ioios-io/pithy/Cases/step/Pithy Screen Plus/Pithy Screen Plus Slanted Stand.step

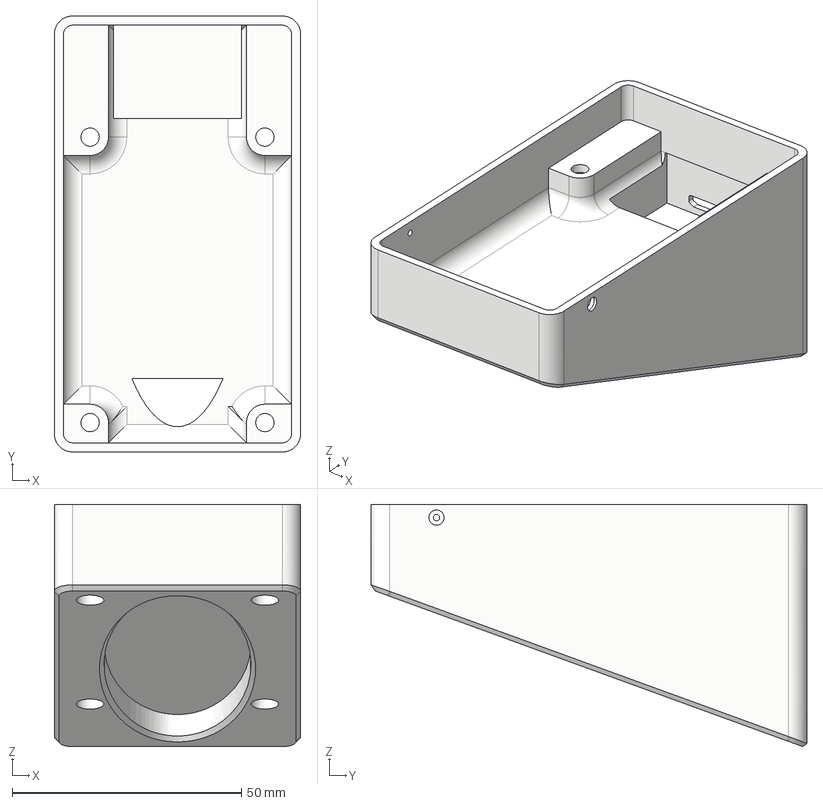
[picture p18: CAD file, 2021-06-20]
Cases/step/Pithy Screen Plus/Pithy Screen Plus Slanted Stand.step
53.7 x 95.0 x 52.8 mm
