ioios-io/pithy/Cases/step/Pithy Screen/Pithy Screen Mount C.step

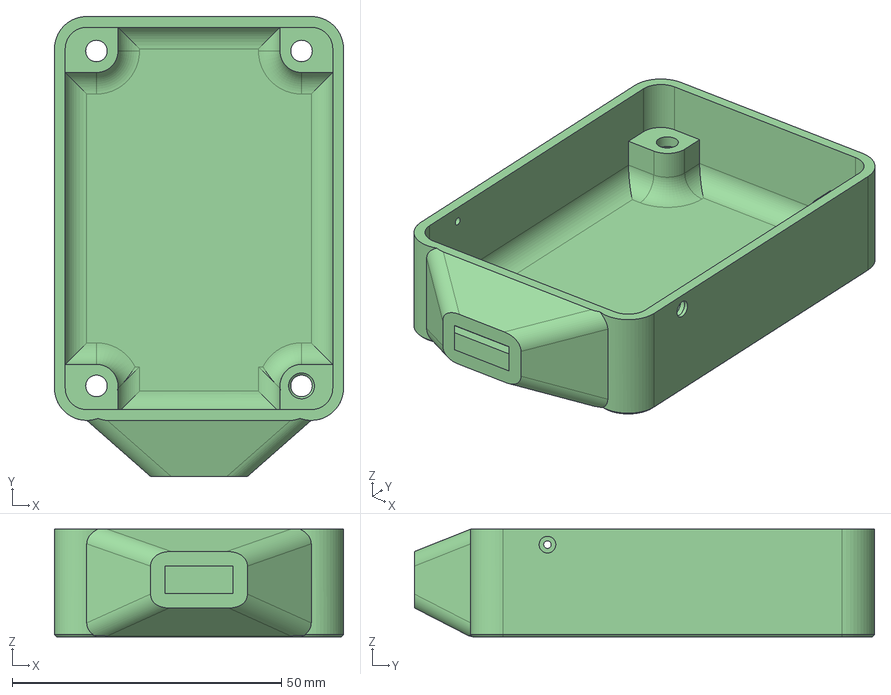
[picture p19: CAD file, 2021-07-11]
Cases/step/Pithy Screen/Pithy Screen Mount C.step
53.7 x 85.5 x 20.0 mm
