ioios-io/pithy/Cases/step/Pithy Dial Plus/Pithy Dial Plus Mount C.step

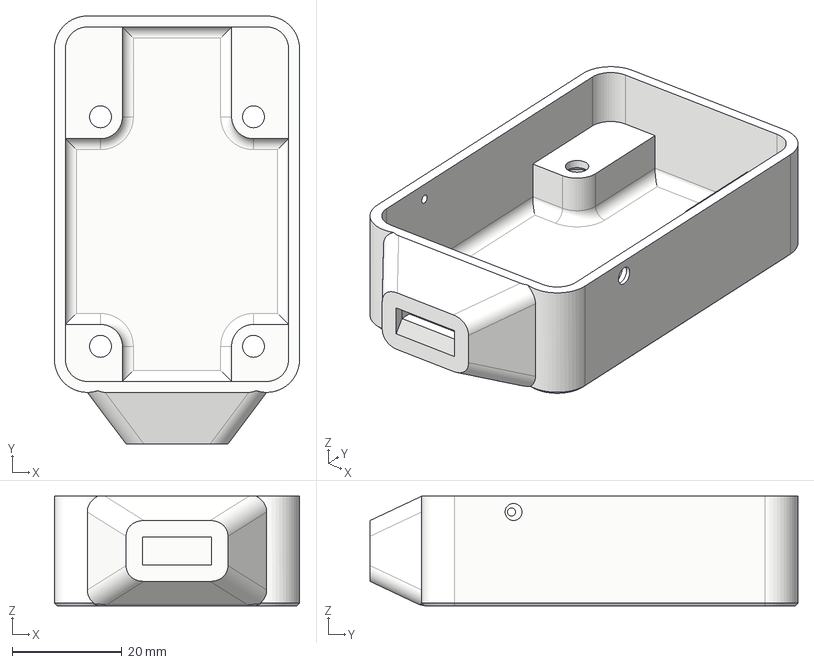
[picture p20: CAD file, 2021-03-28]
Cases/step/Pithy Dial Plus/Pithy Dial Plus Mount C.step
44.8 x 78.2 x 20.0 mm
