ioios-io/pithy/Cases/step/Pithy Dial/Pithy Dial Mount B.step

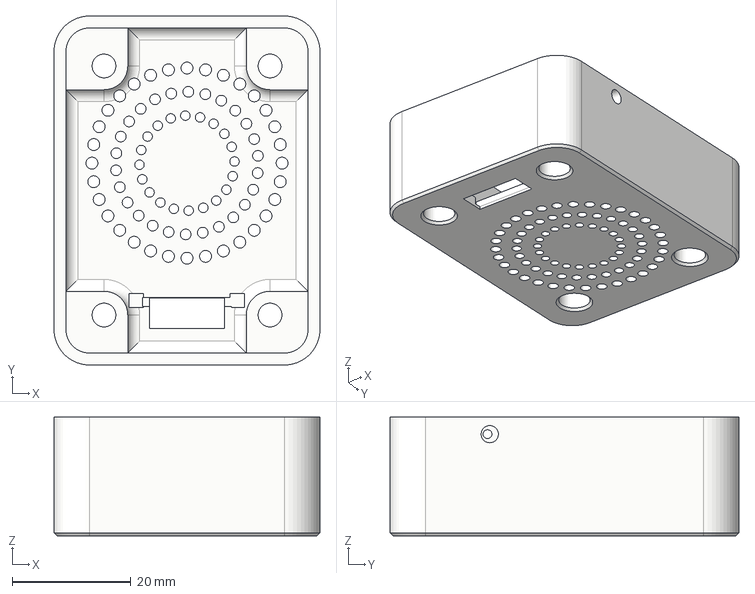
[picture p21: CAD file, 2021-03-28]
Cases/step/Pithy Dial/Pithy Dial Mount B.step
44.8 x 58.7 x 20.0 mm
