ioios-io/pithy/Cases/step/Pithy Pixel Plus/Pithy Pixel Plus Faceplate.step

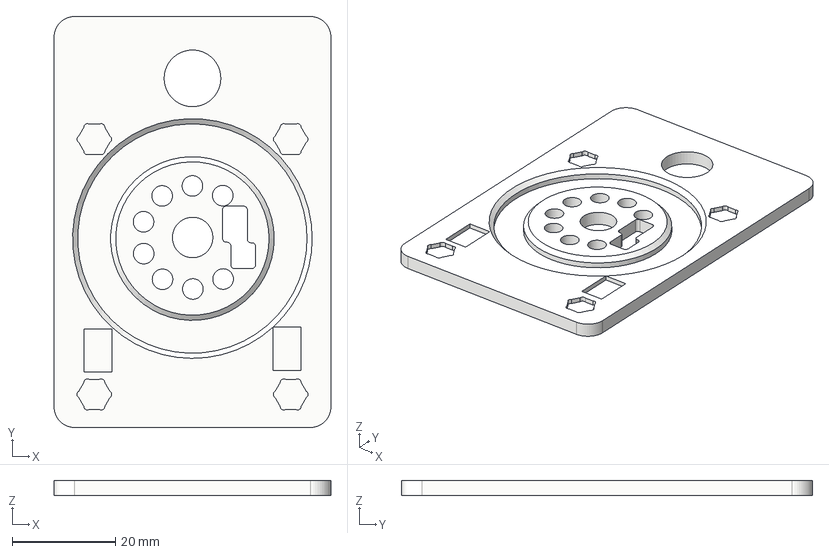
[picture p22: CAD file, 2021-06-11]
Cases/step/Pithy Pixel Plus/Pithy Pixel Plus Faceplate.step
53.7 x 79.8 x 3.00 mm
