ioios-io/pithy/Cases/step/Pithy Pixel/Pithy Pixel Faceplate.step

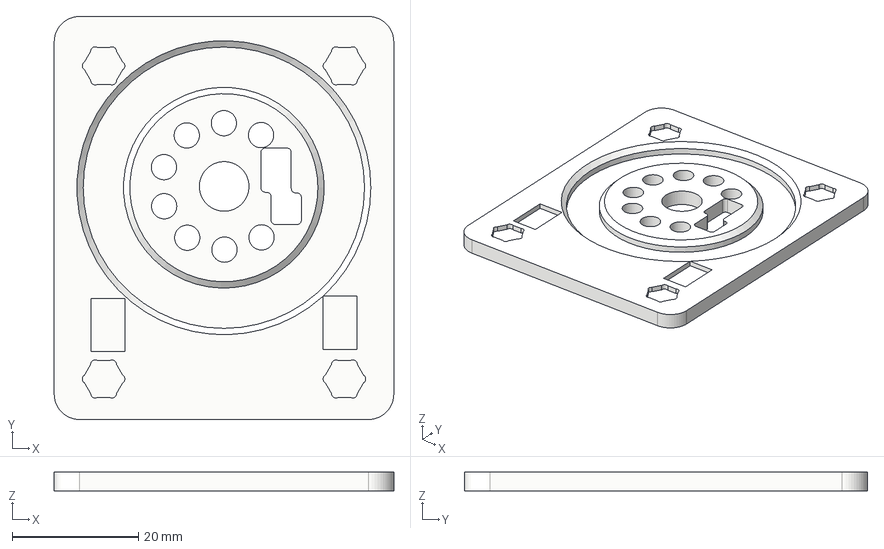
[picture p23: CAD file, 2021-06-11]
Cases/step/Pithy Pixel/Pithy Pixel Faceplate.step
53.7 x 63.8 x 3.00 mm
