ioios-io/pithy/Cases/step/Pithy Screen Plus/Pithy Screen Plus Faceplate.step

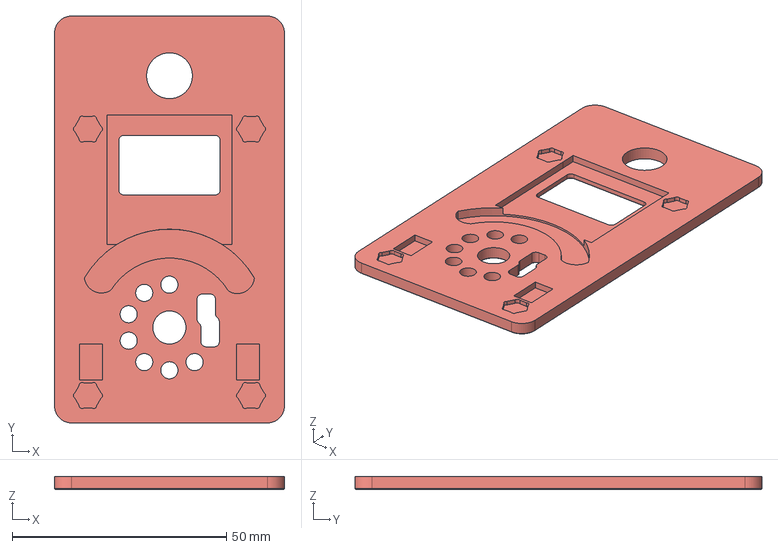
[picture p24: CAD file, 2021-06-11]
Cases/step/Pithy Screen Plus/Pithy Screen Plus Faceplate.step
53.7 x 95.0 x 3.00 mm
