ioios-io/pithy/Cases/step/Pithy Screen/Pithy Screen Mount A.step

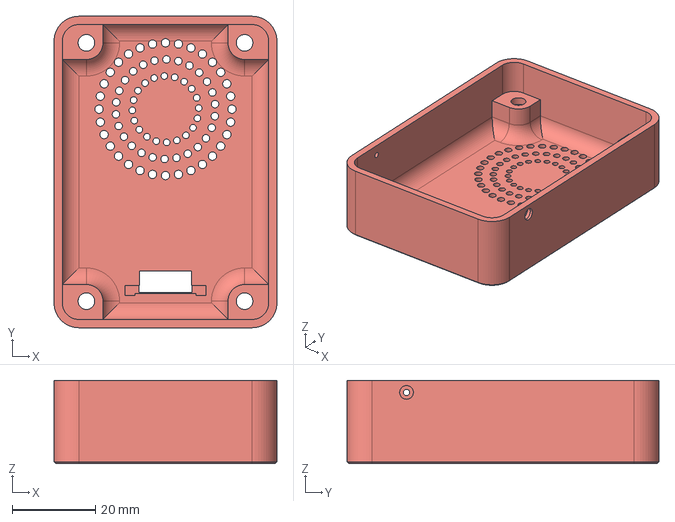
[picture p25: CAD file, 2021-07-11]
Cases/step/Pithy Screen/Pithy Screen Mount A.step
53.7 x 75.0 x 20.0 mm
