ioios-io/pithy/Cases/stl/Pithy Pixel Plus/Printed Knob Standard.stl

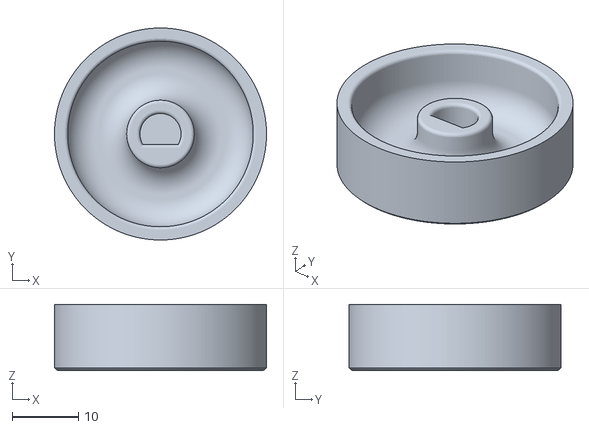
[picture p26: CAD file, 2020-12-21]
Cases/stl/Pithy Pixel Plus/Printed Knob Standard.stl
32.0 x 32.0 x 10.0
