ioios-io/pithy/Cases/stl/Pithy Screen/Printed Knob Standard.stl

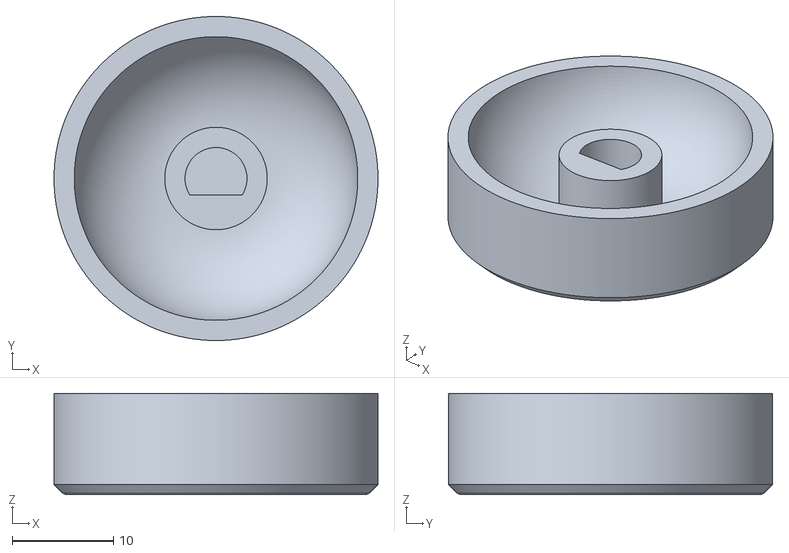
[picture p27: CAD file, 2020-12-08]
Cases/stl/Pithy Screen/Printed Knob Standard.stl
32.0 x 32.0 x 10.0
