ioios-io/pithy/Cases/step/Pithy Dial Plus/Pithy Dial Plus Mount B.step

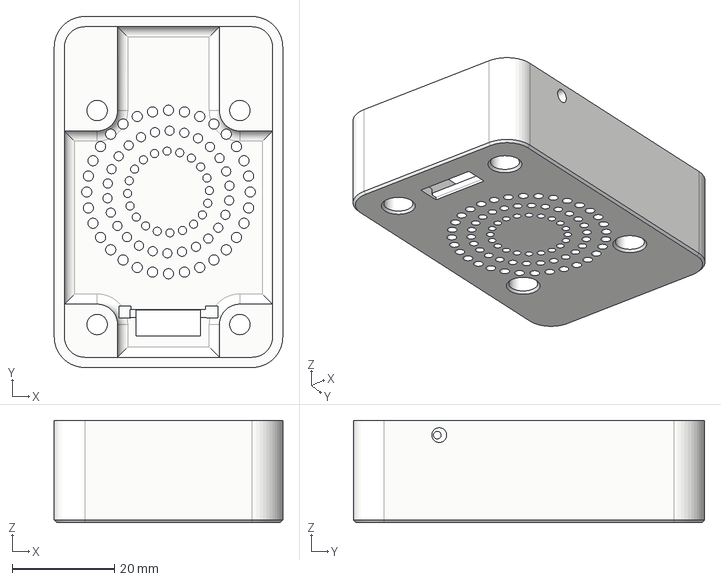
[picture p28: CAD file, 2021-03-28]
Cases/step/Pithy Dial Plus/Pithy Dial Plus Mount B.step
44.8 x 68.7 x 20.0 mm
