ioios-io/pithy/Cases/step/Pithy PIxel Multi Mount.step

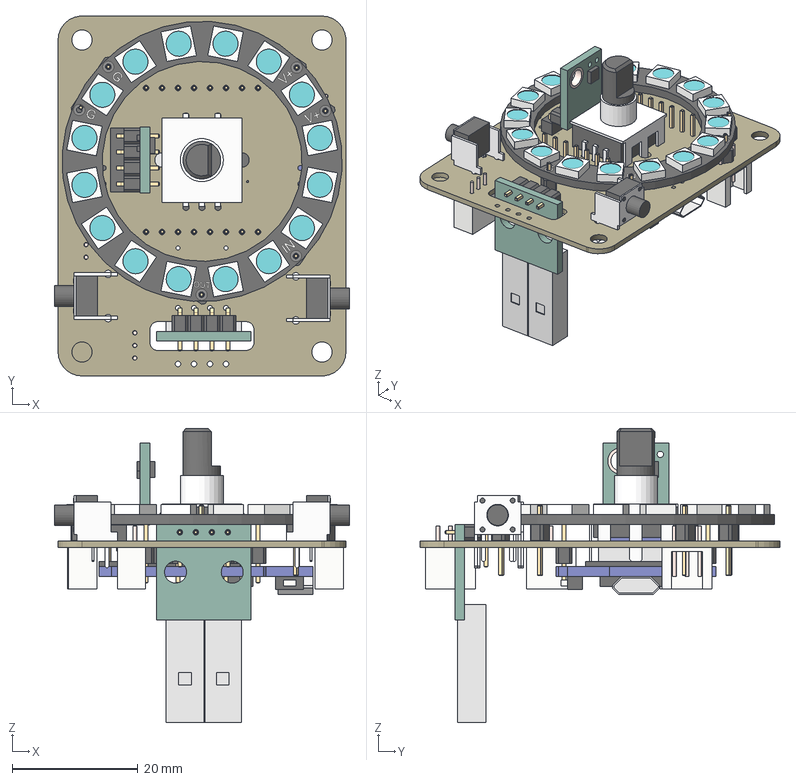
[picture p29: CAD file, 2021-03-28]
Cases/step/Pithy PIxel Multi Mount.step
46.8 x 57.2 x 46.7 mm
Pin Headers Right Angled v5
Board
Neopixel v1 x 16
Pin Headers v7 x 6
PADS_4
Pin Headers v3 x 2
HOLE_3.2 x 4
ROTARY_ENCODER
Pin Headers Right Angled v3
OSHW-LOGO-M
OSHW-LOGO-S
SPDT_RIGHT_ANGLE x 2
