ioios-io/pithy/Cases/step/Pithy Pixel Plus/Pithy Pixel Plus Mount A.step

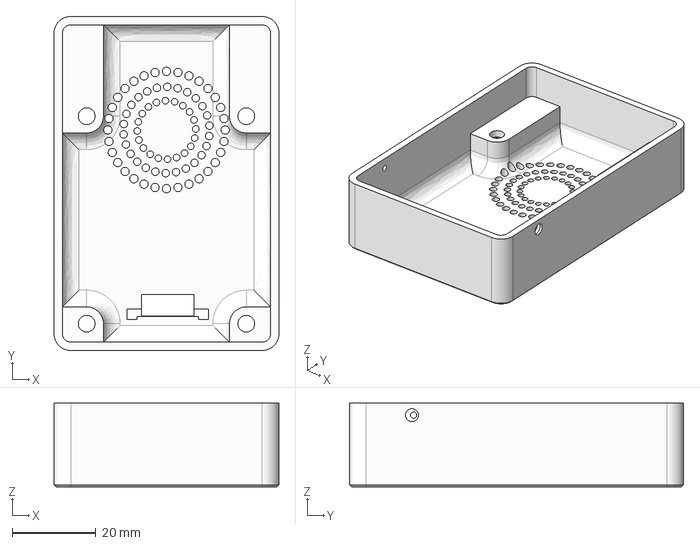
[picture p30: CAD file, 2021-03-28]
Cases/step/Pithy Pixel Plus/Pithy Pixel Plus Mount A.step
53.7 x 79.8 x 20.0 mm
