ioios-io/pithy/Cases/step/Pithy Pixel/Pithy Pixel Mount B.step

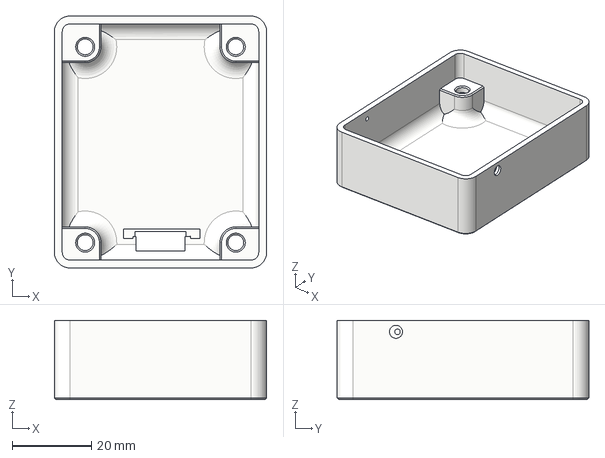
[picture p31: CAD file, 2021-03-28]
Cases/step/Pithy Pixel/Pithy Pixel Mount B.step
53.7 x 63.8 x 20.0 mm
