ioios-io/pithy/Cases/step/Pithy Screen Plus/Pithy Screen Plus Mount B.step

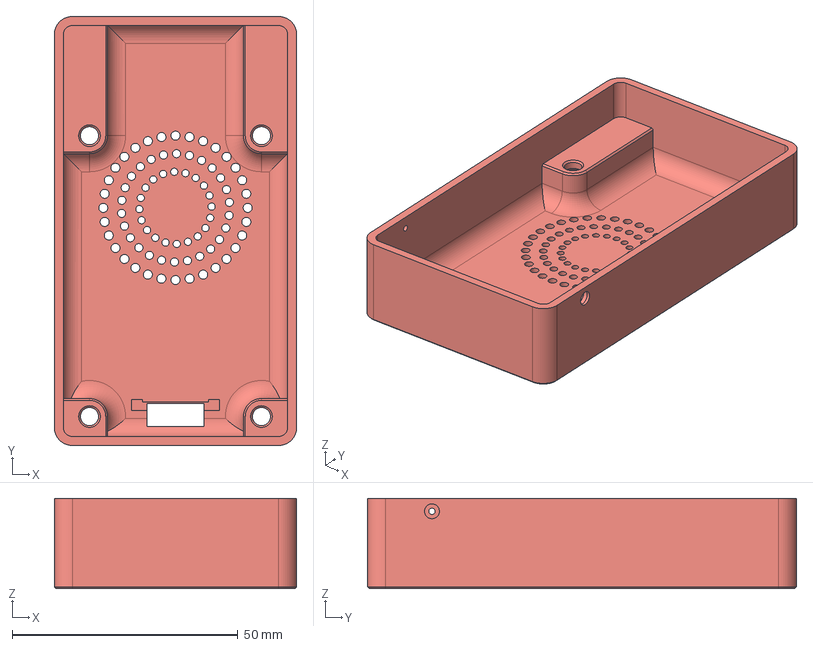
[picture p32: CAD file, 2021-03-28]
Cases/step/Pithy Screen Plus/Pithy Screen Plus Mount B.step
53.7 x 95.0 x 20.0 mm
