ioios-io/pithy/Cases/step/Pithy Screen/Pithy Screen Straight Stand.step

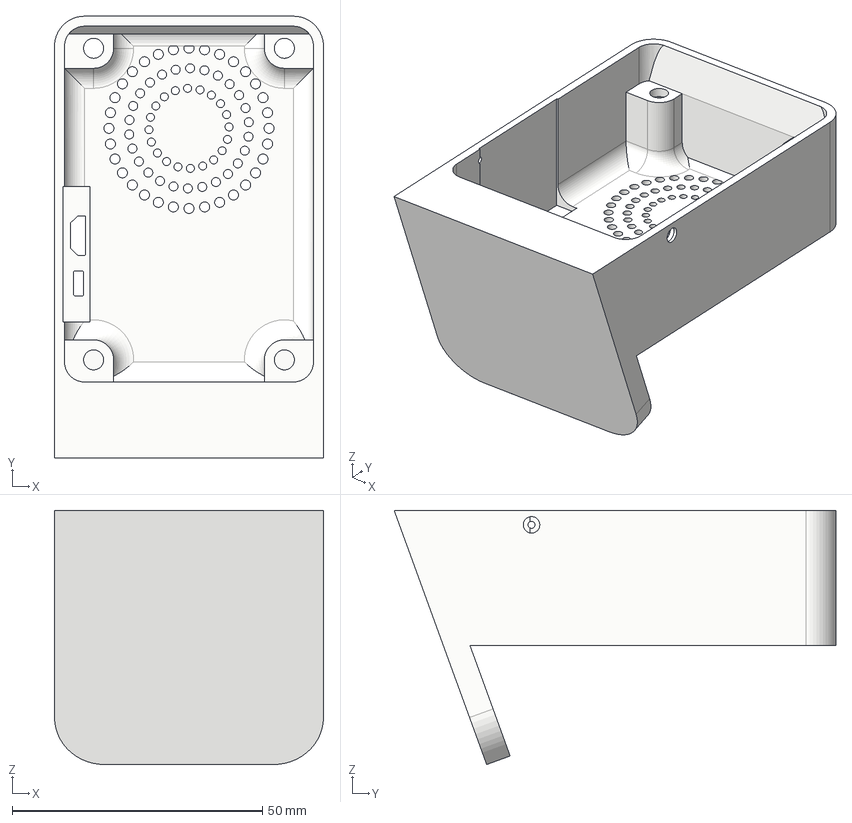
[picture p33: CAD file, 2021-07-03]
Cases/step/Pithy Screen/Pithy Screen Straight Stand.step
53.7 x 88.2 x 50.7 mm
