ioios-io/pithy/Cases/step/Pithy Dial Multi Mount.step

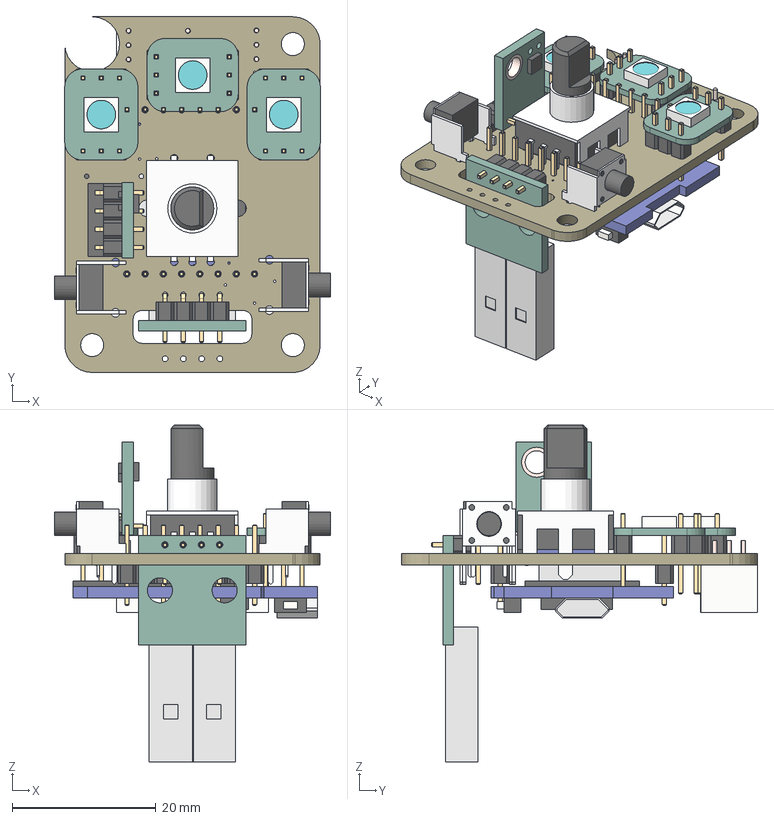
[picture p34: CAD file, 2021-03-28]
Cases/step/Pithy Dial Multi Mount.step
38.5 x 49.6 x 46.9 mm
Board
Pin Headers v3 x 2
HOLE_3.2 x 4
Neopixel v1 x 3
Pin Headers v10 x 6
Pin Headers Right Angled v3
ROTARY_ENCODER
SPDT_RIGHT_ANGLE x 2
OSHW-LOGO-M
OSHW-LOGO-S
Pin Headers Right Angled v5
