ioios-io/pithy/Cases/step/Pithy Dial/Pithy Dial Mount C.step

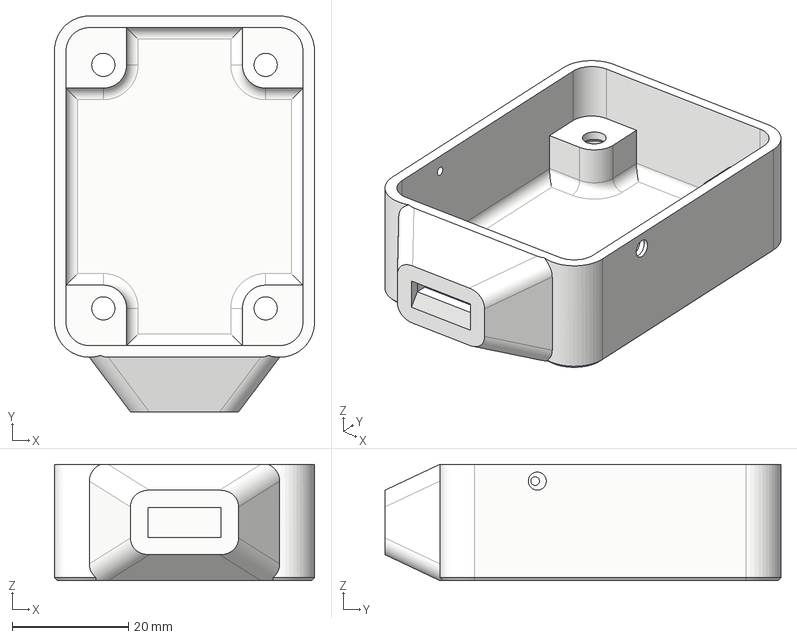
[picture p35: CAD file, 2021-03-28]
Cases/step/Pithy Dial/Pithy Dial Mount C.step
44.8 x 68.2 x 20.0 mm
