ioios-io/pithy/Cases/step/Pithy Pixel/Pithy Pixel Mount C.step

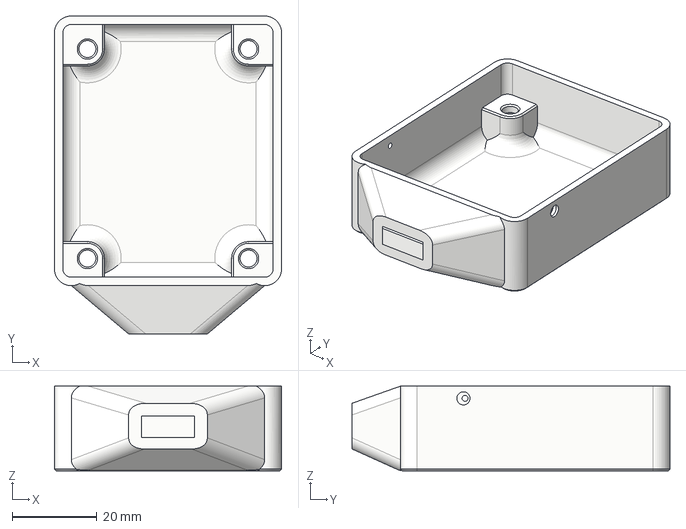
[picture p36: CAD file, 2021-03-28]
Cases/step/Pithy Pixel/Pithy Pixel Mount C.step
53.7 x 75.2 x 20.0 mm
