ioios-io/pithy/Cases/step/Pithy Screen Plus/Pithy Screen Plus Mount C.step

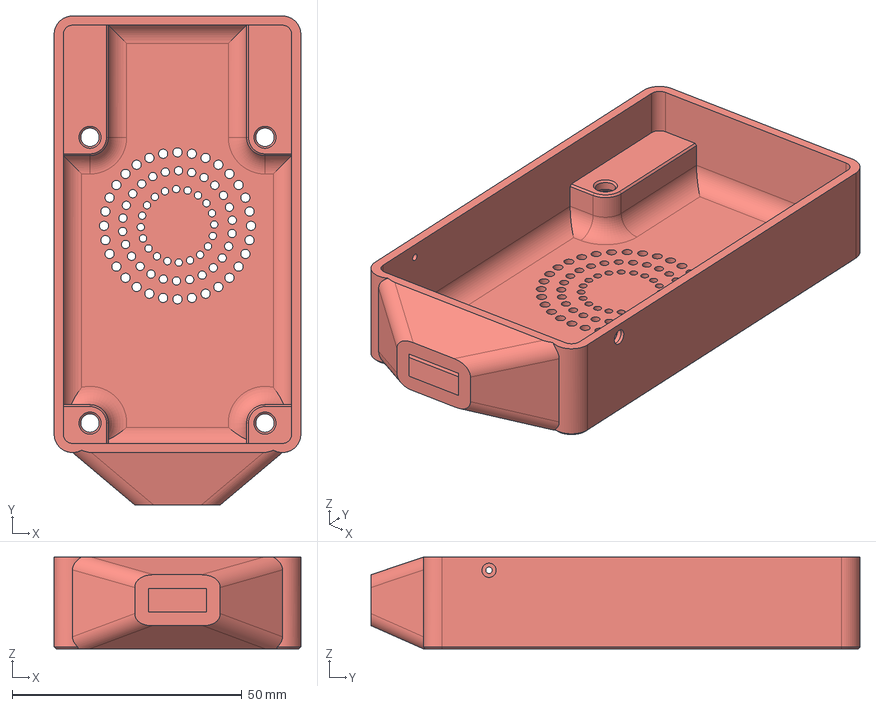
[picture p37: CAD file, 2021-03-28]
Cases/step/Pithy Screen Plus/Pithy Screen Plus Mount C.step
53.7 x 106.5 x 20.0 mm
