ioios-io/pithy/Cases/step/Pithy Screen/Pithy Screen Slanted Stand.step

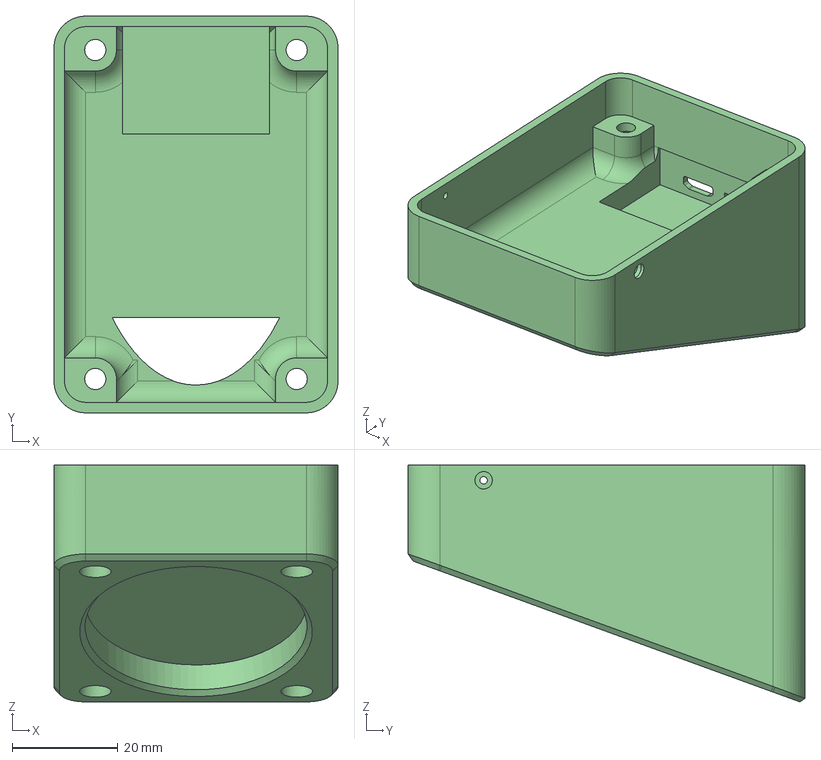
[picture p38: CAD file, 2021-06-20]
Cases/step/Pithy Screen/Pithy Screen Slanted Stand.step
53.7 x 75.0 x 44.8 mm
