ioios-io/pithy/Cases/step/Pithy Pixel Plus/Pithy Pixel Plus Mount D.step

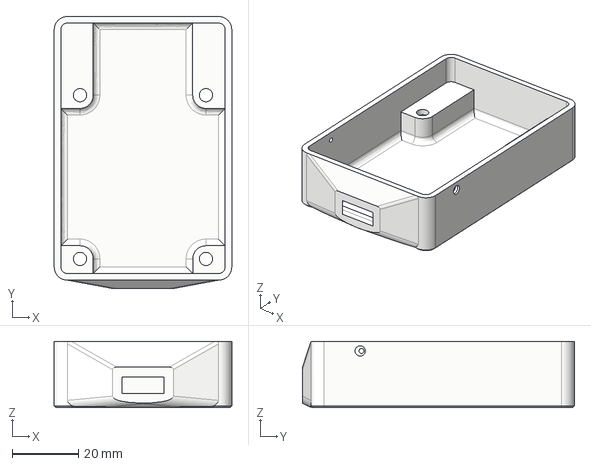
[picture p39: CAD file, 2021-03-28]
Cases/step/Pithy Pixel Plus/Pithy Pixel Plus Mount D.step
53.7 x 82.3 x 20.0 mm
