ioios-io/pithy/Cases/step/Pithy Pixel/Pithy Pixel Mount D.step

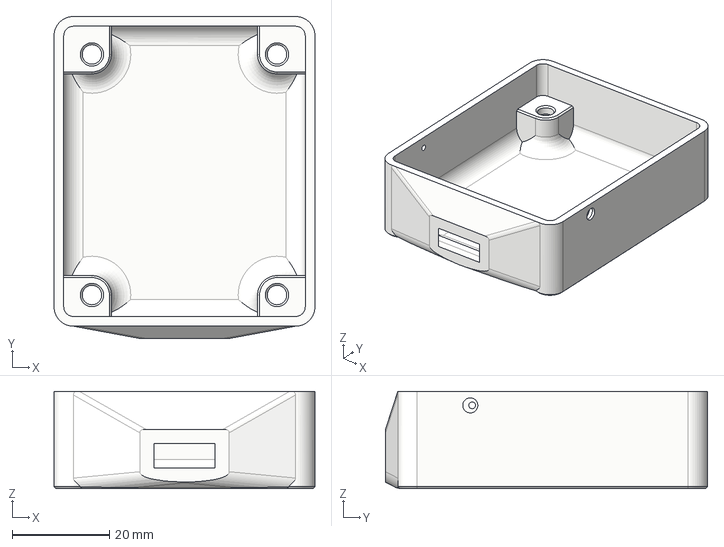
[picture p40: CAD file, 2021-03-28]
Cases/step/Pithy Pixel/Pithy Pixel Mount D.step
53.7 x 66.3 x 20.0 mm
