ioios-io/pithy/Cases/step/Pithy Screen Multi Mount.step

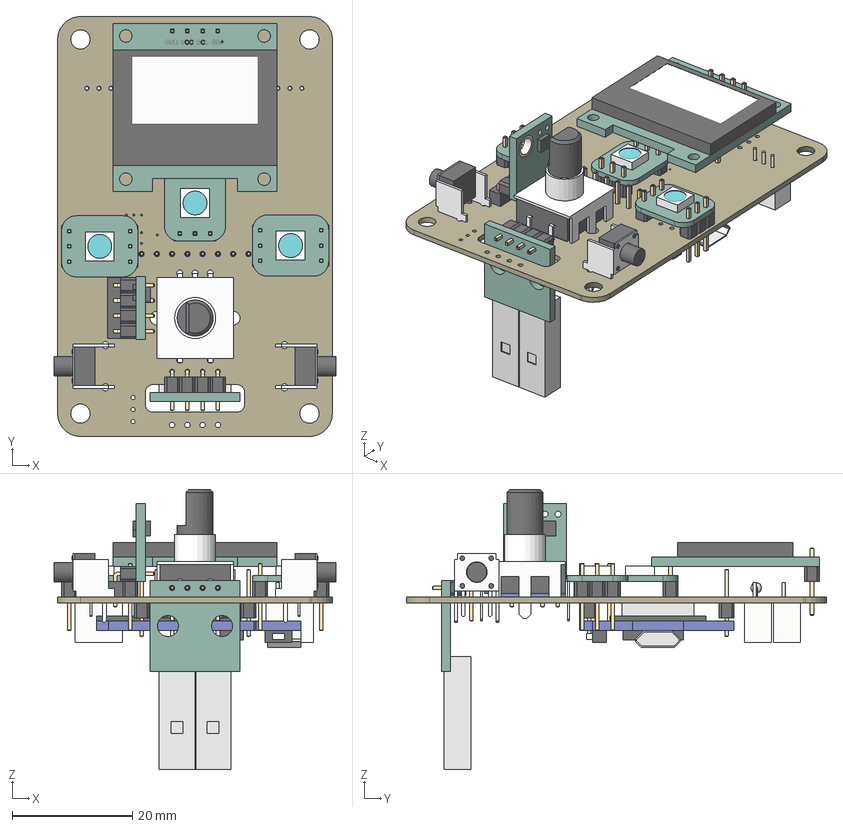
[picture p41: CAD file, 2021-03-28]
Cases/step/Pithy Screen Multi Mount.step
46.8 x 69.9 x 46.6 mm
Board
HOLE_3.2 x 4
ROTARY_ENCODER
1/4W_RESISTOR
Pin Headers v3 x 2
Neopixel v1 x 3
Pin Headers v10 x 6
Pin Headers v2
PADS_4
SPDT_RIGHT_ANGLE x 2
Pin Headers Right Angled v3
OSHW-LOGO-L
OSHW-LOGO-M
OSHW-LOGO-S
Pin Headers Right Angled v5 (2)
