ioios-io/pithy/Cases/step/Pithy Screen Plus/Pithy Screen Plus Mount D.step

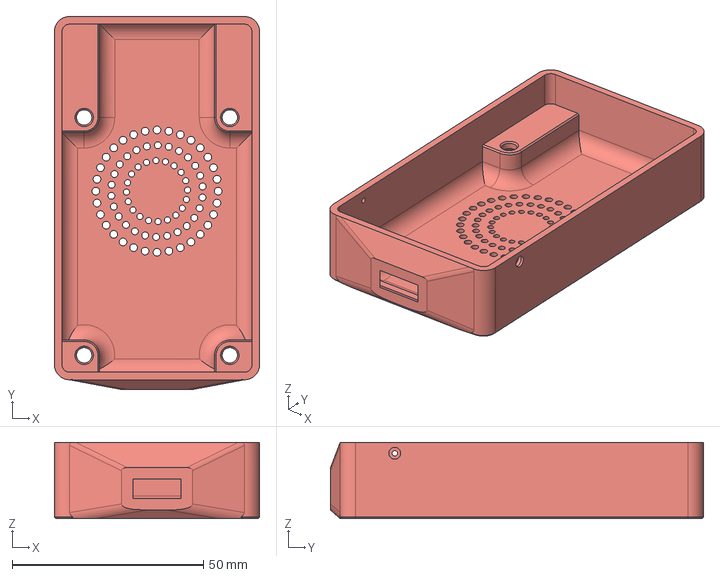
[picture p42: CAD file, 2021-03-28]
Cases/step/Pithy Screen Plus/Pithy Screen Plus Mount D.step
53.7 x 97.6 x 20.0 mm
