ioios-io/pithy/Cases/step/Pithy Screen/Pithy Screen Faceplate.step

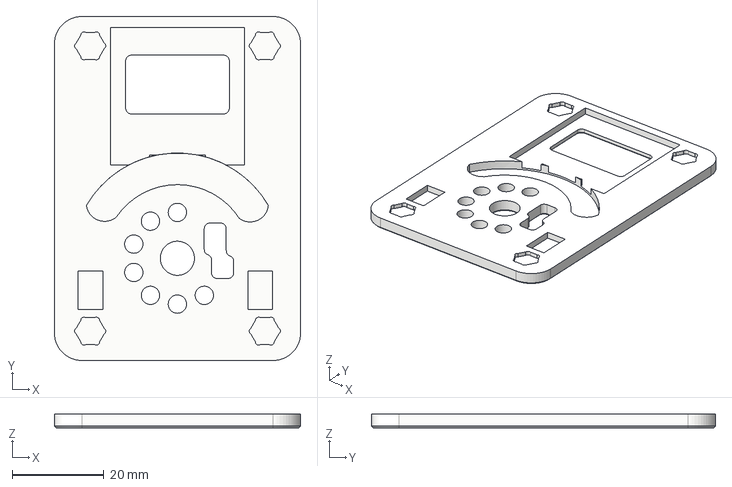
[picture p43: CAD file, 2021-06-11]
Cases/step/Pithy Screen/Pithy Screen Faceplate.step
53.7 x 75.0 x 3.00 mm
