ioios-io/pithy/Cases/step/Pithy Pixel Plus/Pithy Pixel Plus Mount C.step

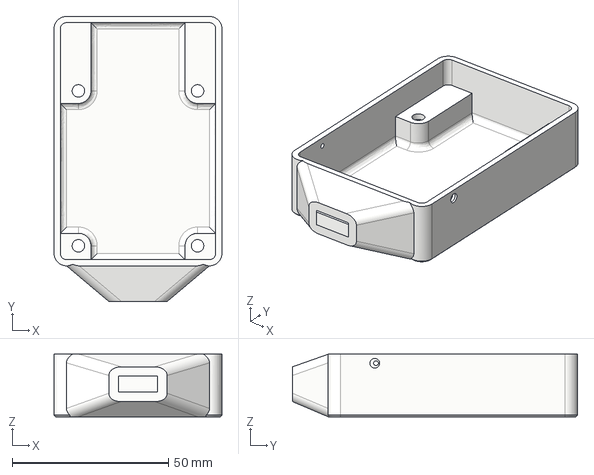
[picture p44: CAD file, 2021-03-28]
Cases/step/Pithy Pixel Plus/Pithy Pixel Plus Mount C.step
53.7 x 91.2 x 20.0 mm
